Tony1547/Tony-s-dev-board/CAD/Tony's devboard 1/Tony's devboard 1 - USB_C_Receptacle_GCT_USB4105-xx-A_16P_TopMnt_Horizontal (10).stl

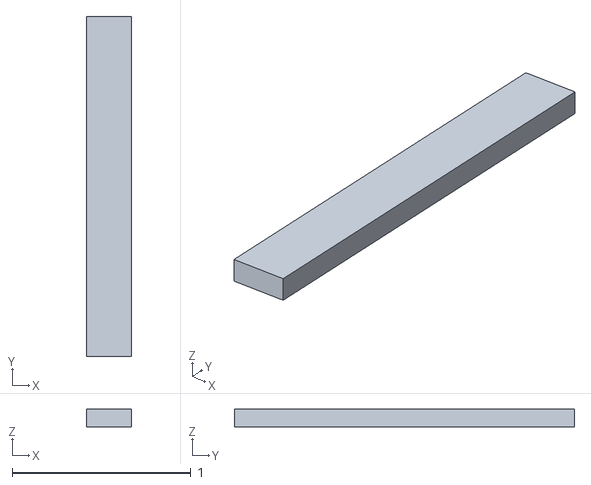
[picture p6: CAD file, 2025-11-30]
CAD/Tony's devboard 1/Tony's devboard 1 - USB_C_Receptacle_GCT_USB4105-xx-A_16P_TopMnt_Horizontal (10).stl
0.25 x 1.90 x 0.1
