Tony1547/Tony-s-dev-board/CAD/Tony's devboard 1/Tony's devboard 1 - USB_C_Receptacle_GCT_USB4105-xx-A_16P_TopMnt_Horizontal (19).stl

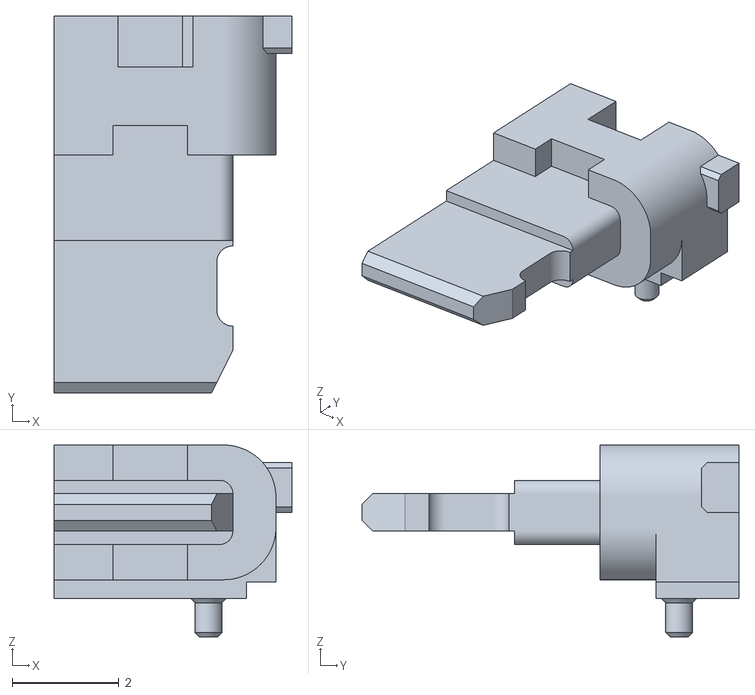
[picture p7: CAD file, 2025-11-30]
CAD/Tony's devboard 1/Tony's devboard 1 - USB_C_Receptacle_GCT_USB4105-xx-A_16P_TopMnt_Horizontal (19).stl
4.45 x 7.05 x 3.59
