Tony1547/Tony-s-dev-board/CAD/Tony's devboard 1/Tony's devboard 1 - Tony's devboard_PCB.stl

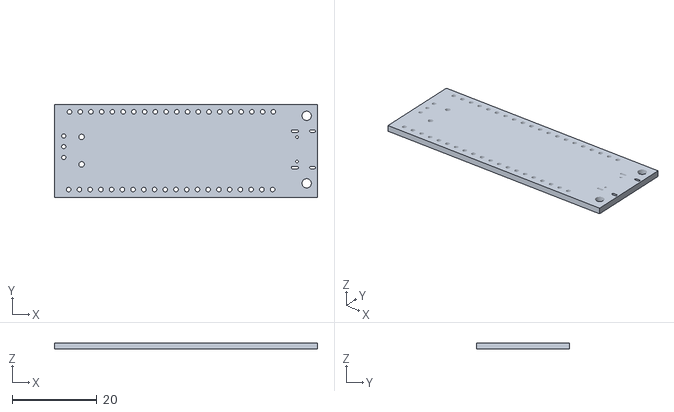
[picture p8: CAD file, 2025-11-30]
CAD/Tony's devboard 1/Tony's devboard 1 - Tony's devboard_PCB.stl
62.2 x 22.0 x 1.51
