Tony1547/Tony-s-dev-board/CAD/Tony's devboard 1/Tony's devboard 1 - USB_C_Receptacle_GCT_USB4105-xx-A_16P_TopMnt_Horizontal (22).stl

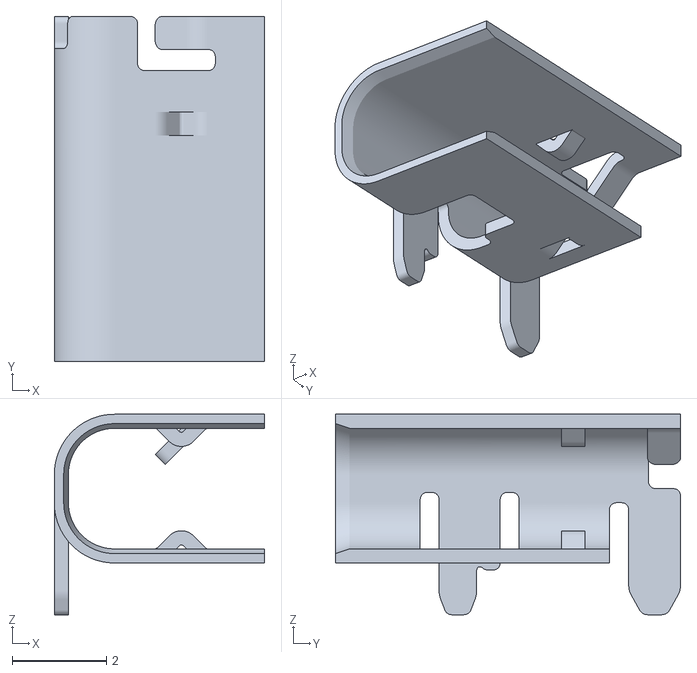
[picture p9: CAD file, 2025-11-30]
CAD/Tony's devboard 1/Tony's devboard 1 - USB_C_Receptacle_GCT_USB4105-xx-A_16P_TopMnt_Horizontal (22).stl
4.47 x 7.33 x 4.26
