Tony1547/Tony-s-dev-board/CAD/Tony's devboard 1/Tony's devboard 1 - PinHeader_1x03_P2.54mm_Vertical.stl

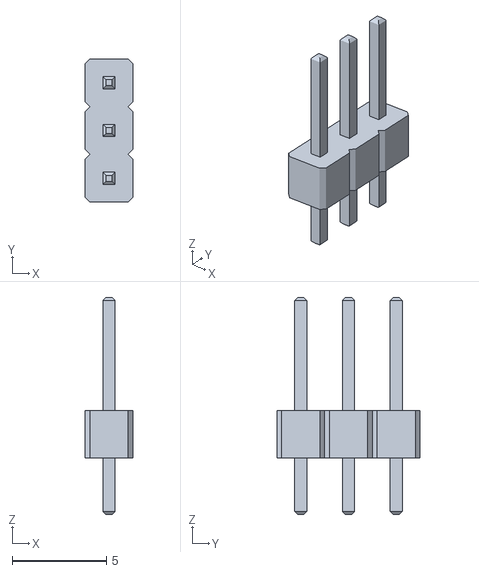
[picture p10: CAD file, 2025-11-30]
CAD/Tony's devboard 1/Tony's devboard 1 - PinHeader_1x03_P2.54mm_Vertical.stl
2.54 x 7.62 x 11.5
