Tony1547/Tony-s-dev-board/CAD/Tony's devboard 1/Tony's devboard 1 - R_0201_0603Metric.stl

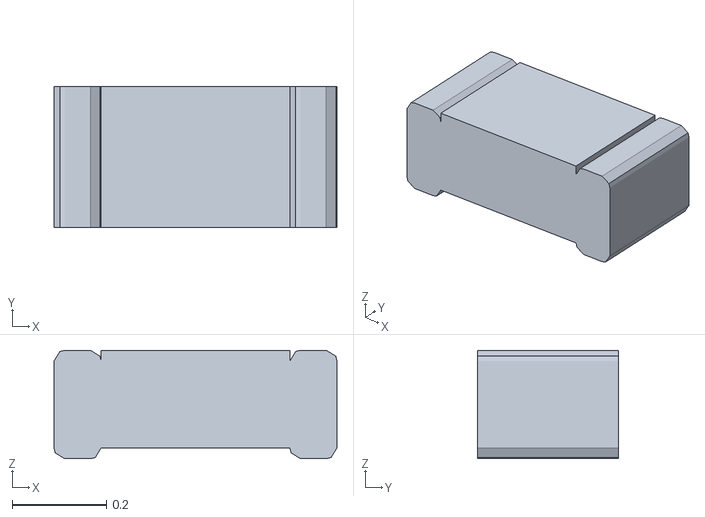
[picture p11: CAD file, 2025-11-30]
CAD/Tony's devboard 1/Tony's devboard 1 - R_0201_0603Metric.stl
0.6 x 0.3 x 0.23
