Tony1547/Tony-s-dev-board/CAD/Tony's devboard 1/Tony's devboard 1 - Crystal_SMD_0603-4Pin_6.0x3.5mm.stl

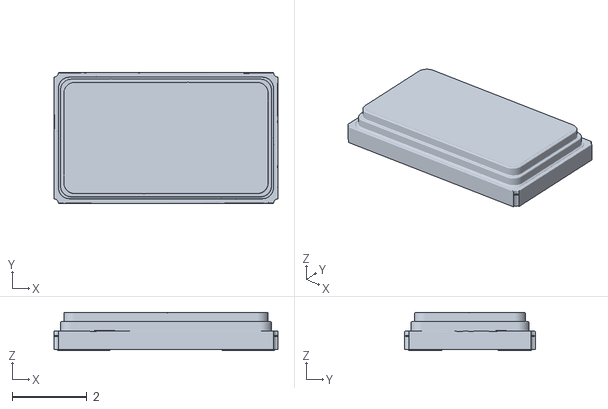
[picture p12: CAD file, 2025-11-30]
CAD/Tony's devboard 1/Tony's devboard 1 - Crystal_SMD_0603-4Pin_6.0x3.5mm.stl
6.00 x 3.50 x 1.03
