Tony1547/Tony-s-dev-board/CAD/Tony's devboard 1/Tony's devboard 1 - Part 2.stl

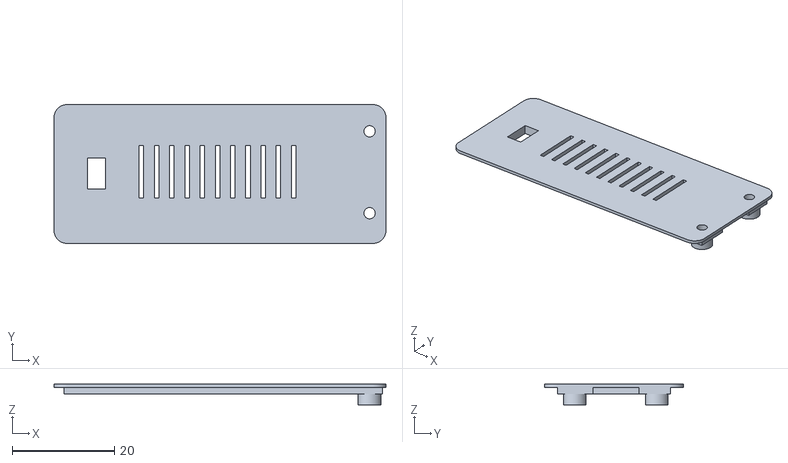
[picture p13: CAD file, 2025-11-30]
CAD/Tony's devboard 1/Tony's devboard 1 - Part 2.stl
64.8 x 27.1 x 4.03
