Tony1547/Tony-s-dev-board/CAD/Tony's devboard 1/Tony's devboard 1 - SW_PUSH_1P1T_6x3.5mm_H5.0_APEM_MJTP1250.stl

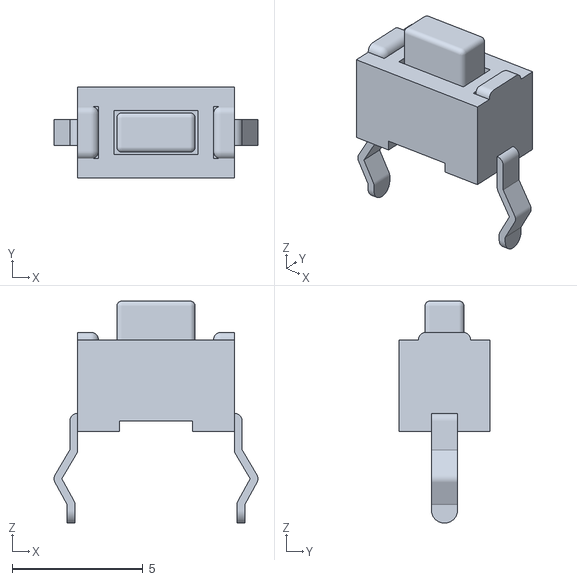
[picture p14: CAD file, 2025-11-30]
CAD/Tony's devboard 1/Tony's devboard 1 - SW_PUSH_1P1T_6x3.5mm_H5.0_APEM_MJTP1250.stl
7.81 x 3.50 x 8.50
