Tony1547/Tony-s-dev-board/CAD/Tony's devboard 1/Tony's devboard 1 - SOT-223.stl

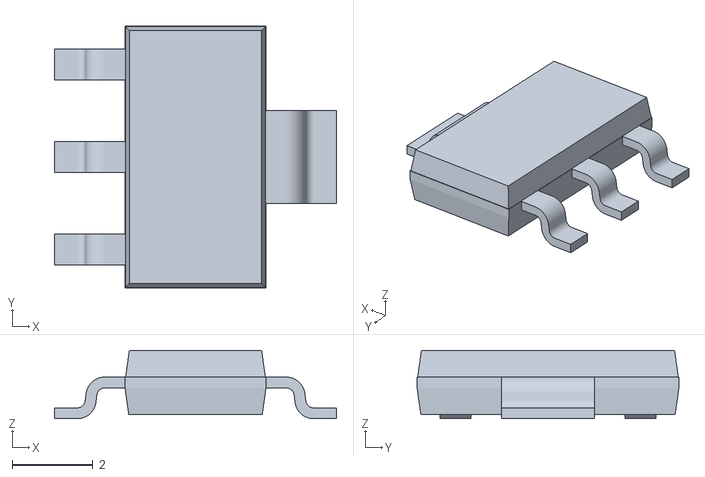
[picture p15: CAD file, 2025-11-30]
CAD/Tony's devboard 1/Tony's devboard 1 - SOT-223.stl
7.00 x 6.50 x 1.70
