Tony1547/Tony-s-dev-board/CAD/Tony's devboard 1/Tony's devboard 1 - Part 3.stl

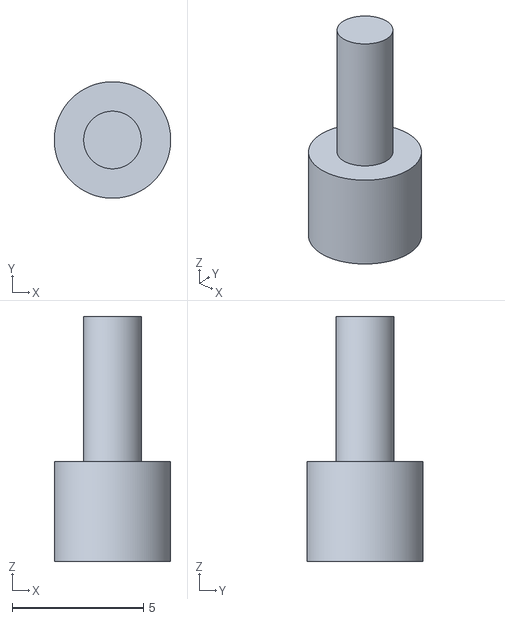
[picture p17: CAD file, 2025-11-30]
CAD/Tony's devboard 1/Tony's devboard 1 - Part 3.stl
4.44 x 4.44 x 9.35
