Tony1547/Tony-s-dev-board/CAD/Tony's devboard 1/Tony's devboard 1 - SOIC-8_5.3x5.3mm_P1.27mm.stl

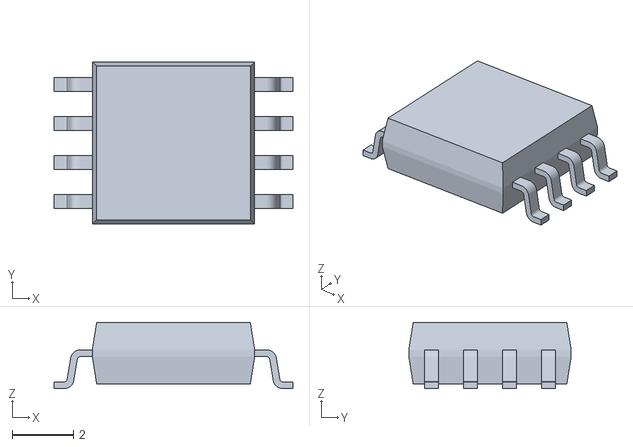
[picture p18: CAD file, 2025-11-30]
CAD/Tony's devboard 1/Tony's devboard 1 - SOIC-8_5.3x5.3mm_P1.27mm.stl
7.80 x 5.30 x 2.16
