Tony1547/Tony-s-dev-board/CAD/Tony's devboard 1/Tony's devboard 1 - Part 1.stl

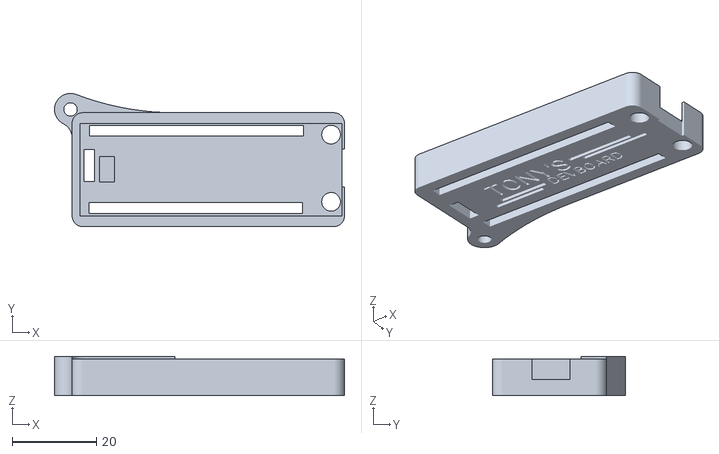
[picture p19: CAD file, 2025-11-30]
CAD/Tony's devboard 1/Tony's devboard 1 - Part 1.stl
69.0 x 31.7 x 9.35
