Tony1547/Tony-s-dev-board/CAD/Tony's devboard 1/Tony's devboard 1 - QFN-56-1EP_7x7mm_P0.4mm_EP3.2x3.2mm.stl

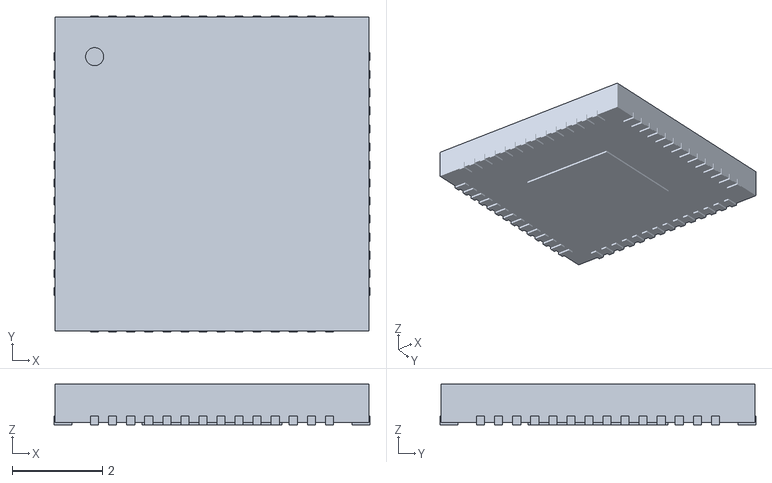
[picture p20: CAD file, 2025-11-30]
CAD/Tony's devboard 1/Tony's devboard 1 - QFN-56-1EP_7x7mm_P0.4mm_EP3.2x3.2mm.stl
7.00 x 7.00 x 0.9
